Uspizig/WifiWallSwitch/Pictures/230V Module/IMG20230703215954.jpg

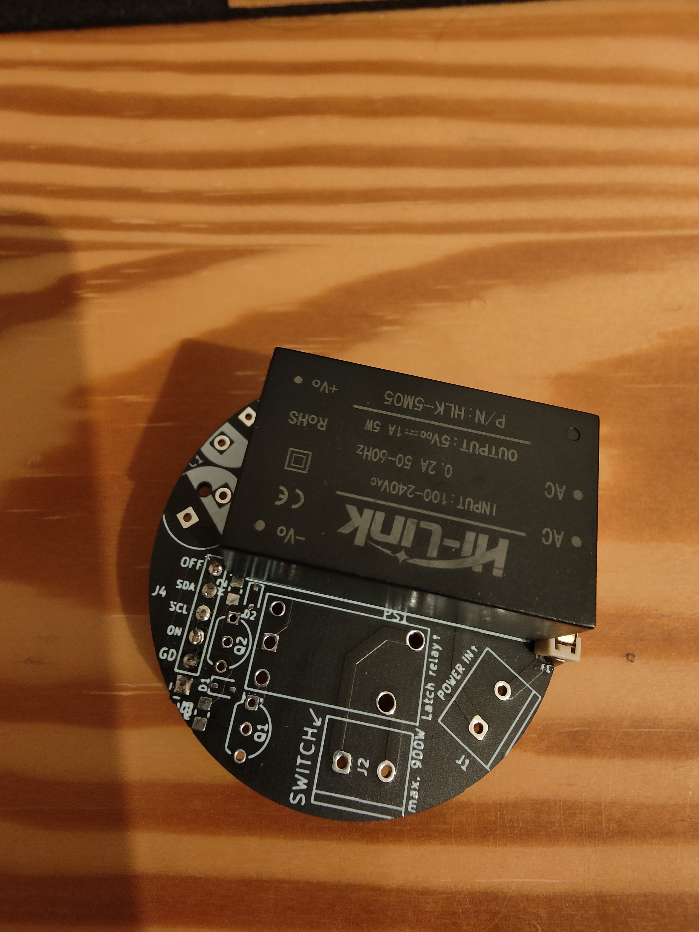
Pictures/230V Module/IMG20230703215954.jpg
