Uspizig/WifiWallSwitch/Pictures/230V Module/IMG20230703220000.jpg

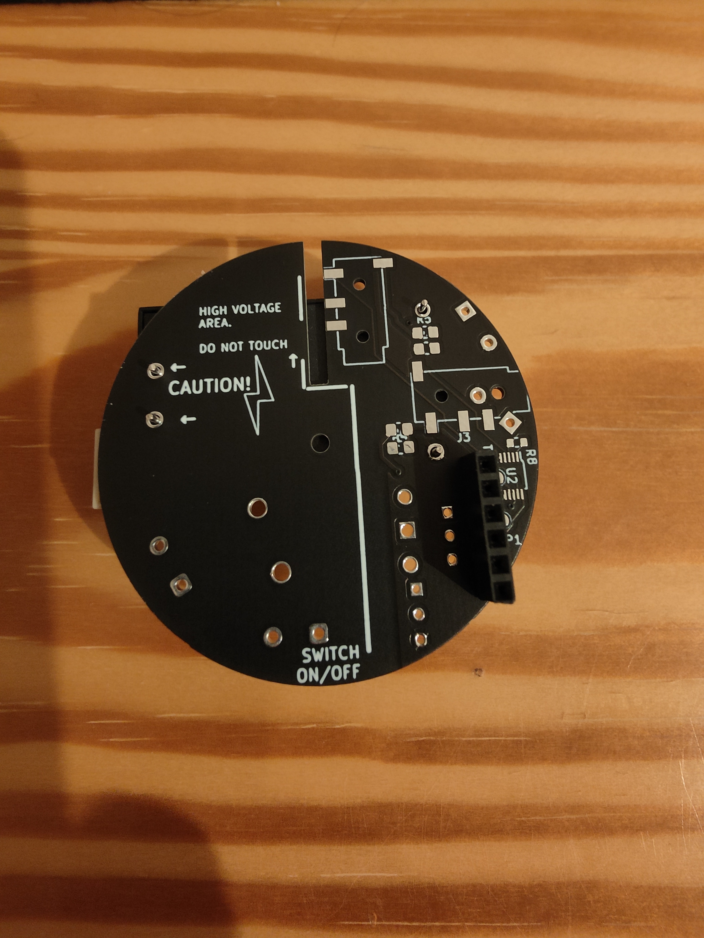
Pictures/230V Module/IMG20230703220000.jpg
