Uspizig/WifiWallSwitch/Pictures/230V Module/IMG20230703220749.jpg

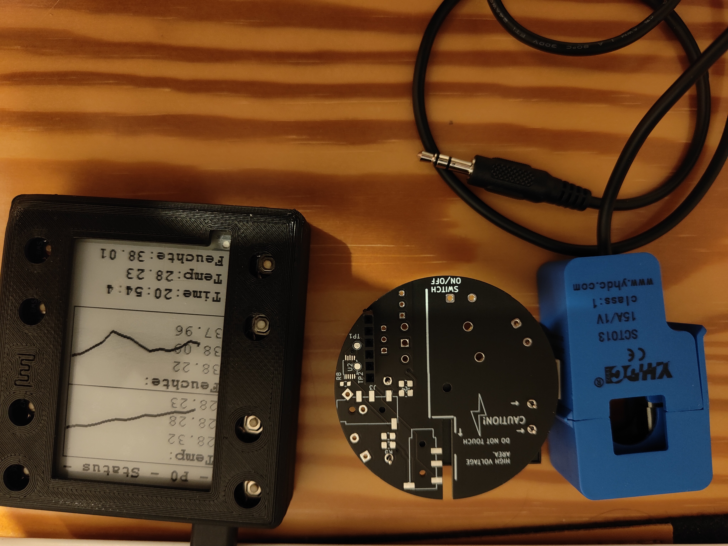
Pictures/230V Module/IMG20230703220749.jpg
