Uspizig/WifiWallSwitch/Pictures/230V Module/IMG20230703220805.jpg

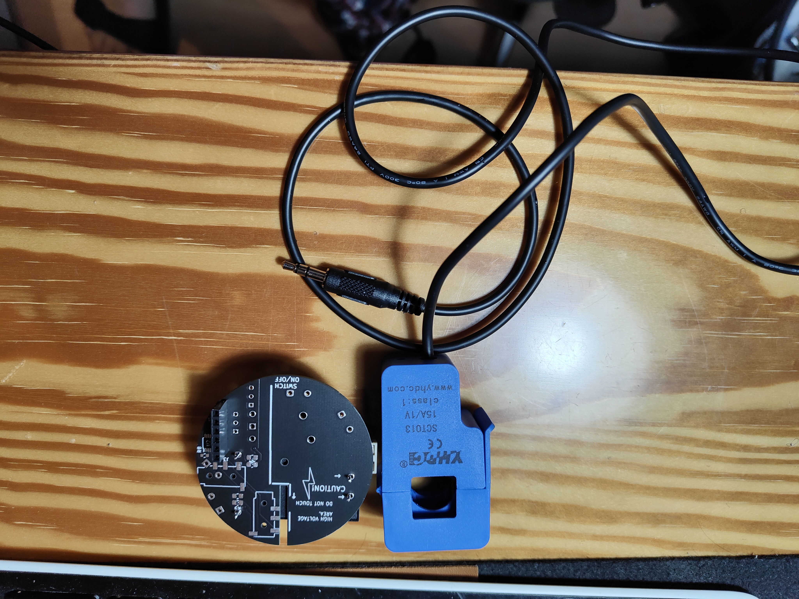
Pictures/230V Module/IMG20230703220805.jpg
