Uspizig/WifiWallSwitch/Pictures/230V Module/IMG20230703220815.jpg

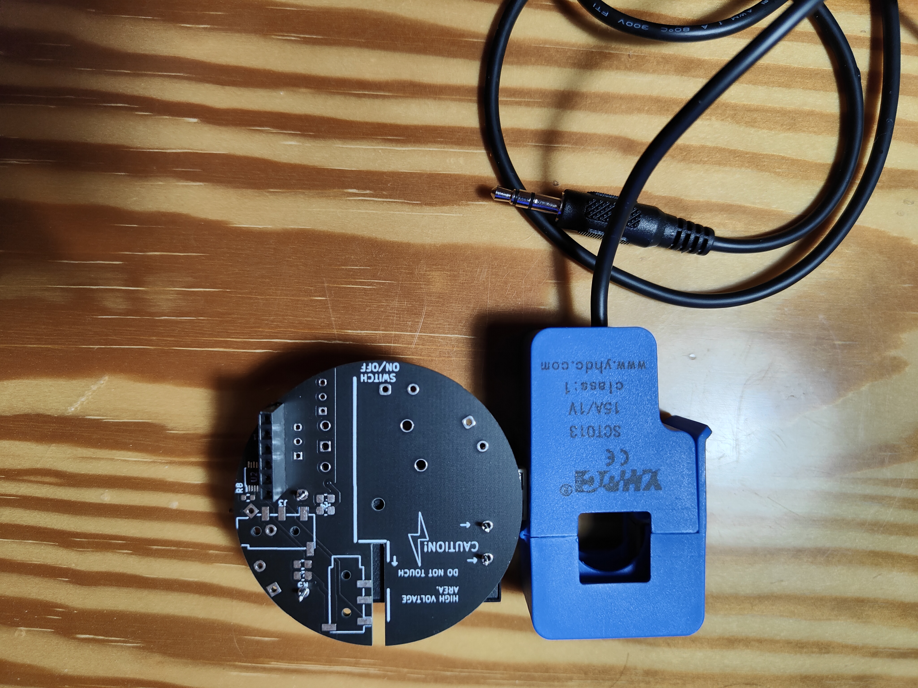
Pictures/230V Module/IMG20230703220815.jpg
