Uspizig/WifiWallSwitch/Pictures/230V Module/IMG20230703220847.jpg

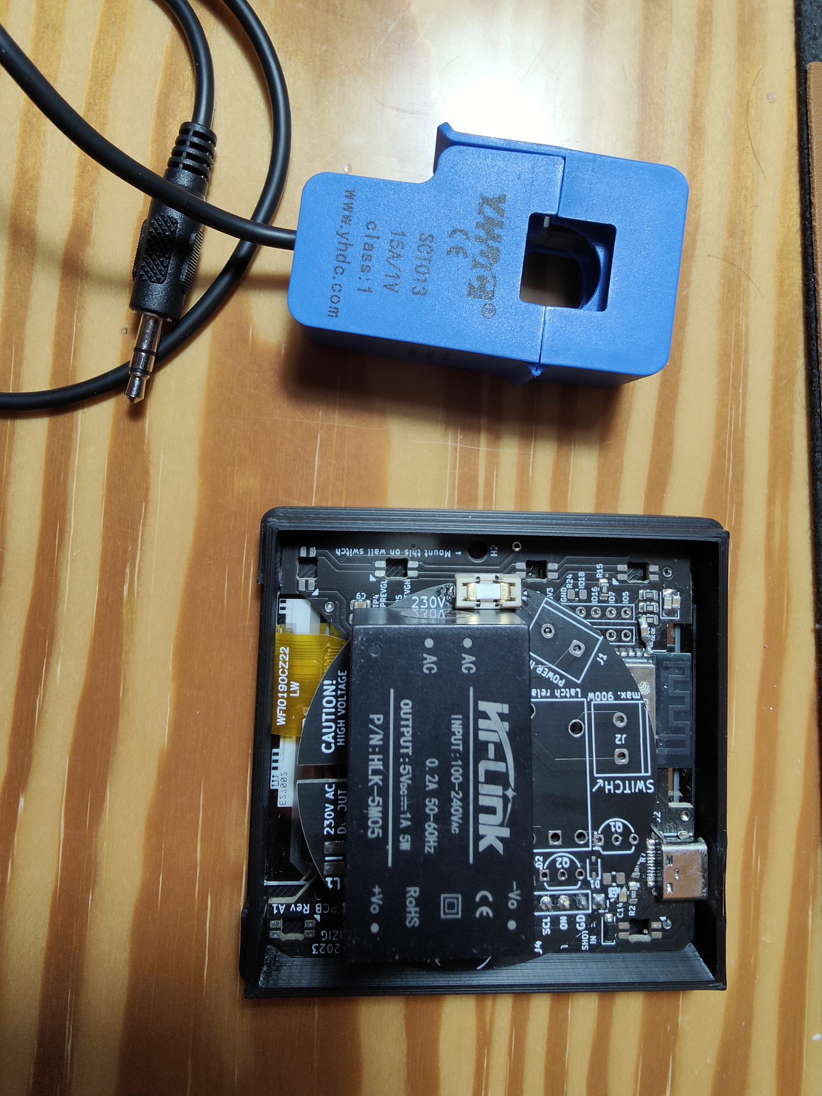
Pictures/230V Module/IMG20230703220847.jpg
