Uspizig/WifiWallSwitch/Pictures/230V Module/IMG20230703220852.jpg

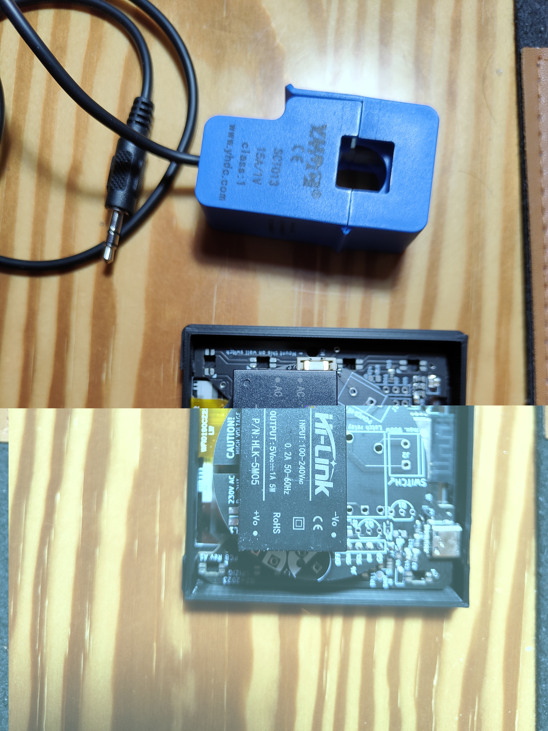
Pictures/230V Module/IMG20230703220852.jpg
