Uspizig/WifiWallSwitch/Pictures/ArduinoBlackCaseButtons/Black.jpg

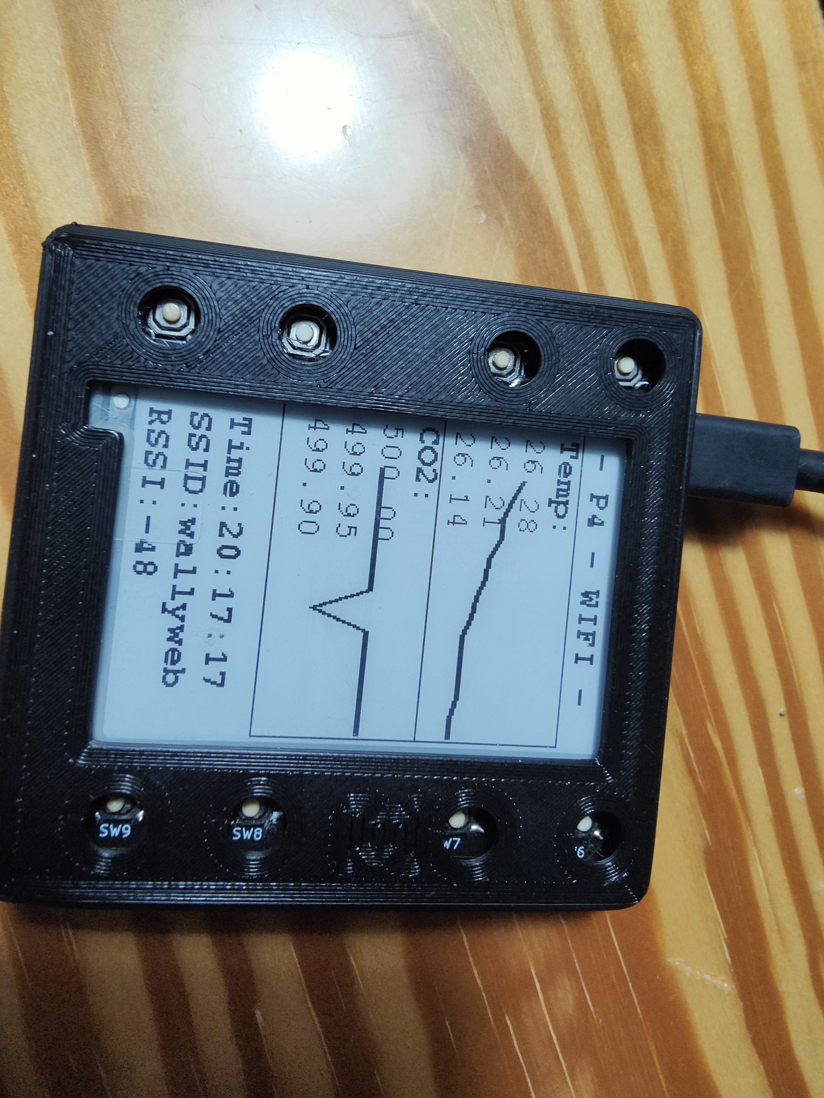
Pictures/ArduinoBlackCaseButtons/Black.jpg
