Uspizig/WifiWallSwitch/Pictures/ArduinoBlackCaseButtons/IMG20230702214540.jpg

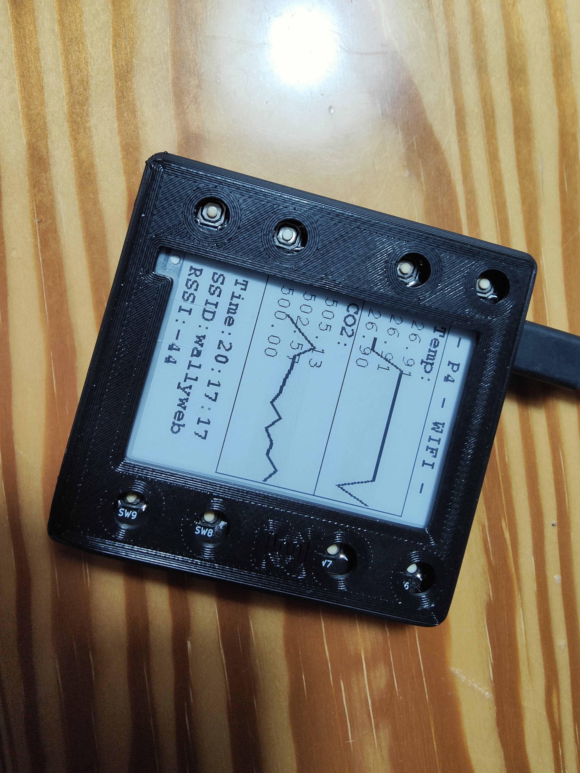
Pictures/ArduinoBlackCaseButtons/IMG20230702214540.jpg
