Uspizig/WifiWallSwitch/Pictures/ArduinoBlackCaseButtons/IMG20230702214551.jpg

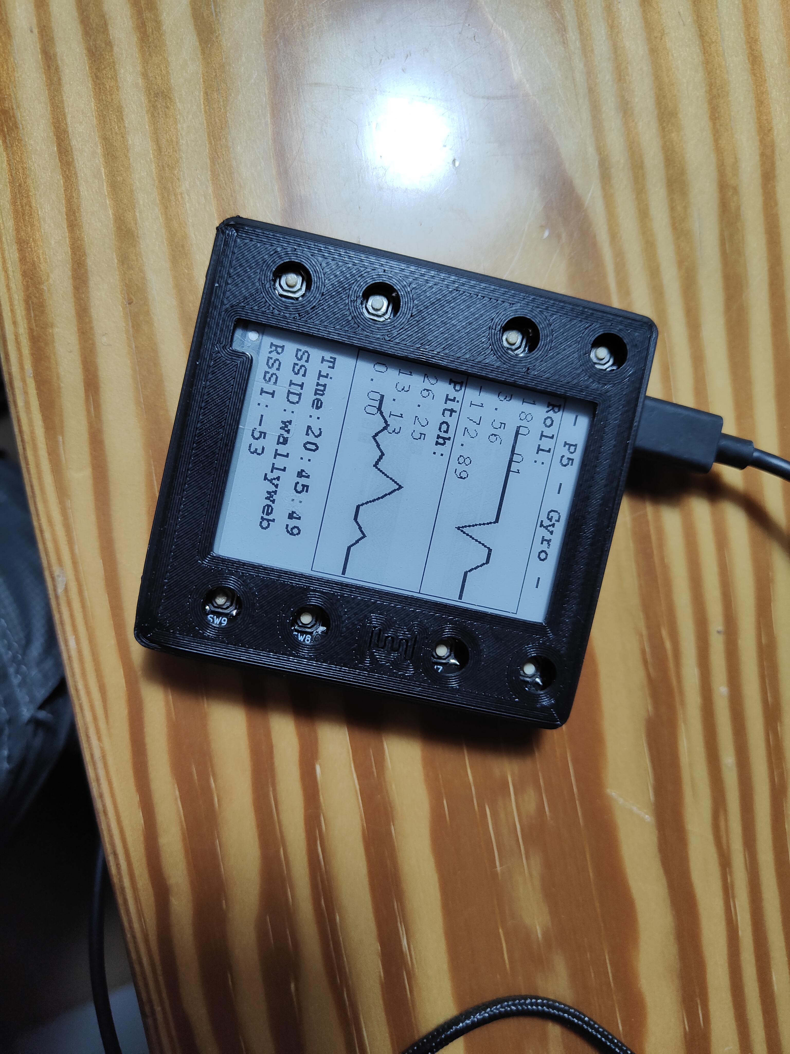
Pictures/ArduinoBlackCaseButtons/IMG20230702214551.jpg
