Uspizig/WifiWallSwitch/Pictures/ArduinoBlackCaseButtons/IMG20230702214604.jpg

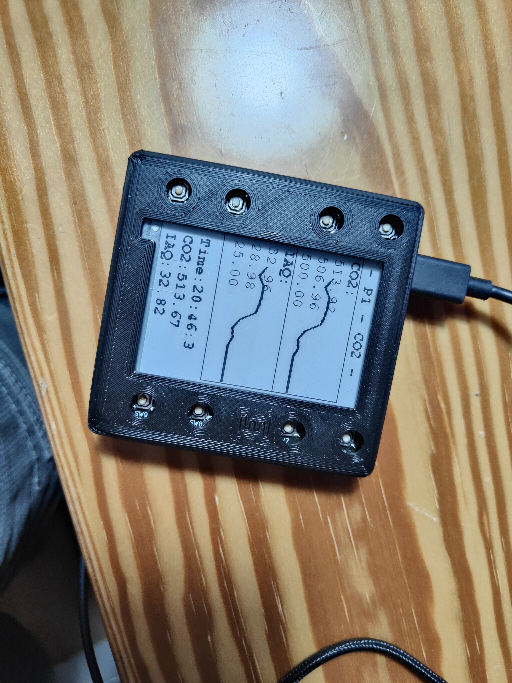
Pictures/ArduinoBlackCaseButtons/IMG20230702214604.jpg
