Uspizig/WifiWallSwitch/Pictures/ArduinoBlackCaseButtons/IMG20230702214607.jpg

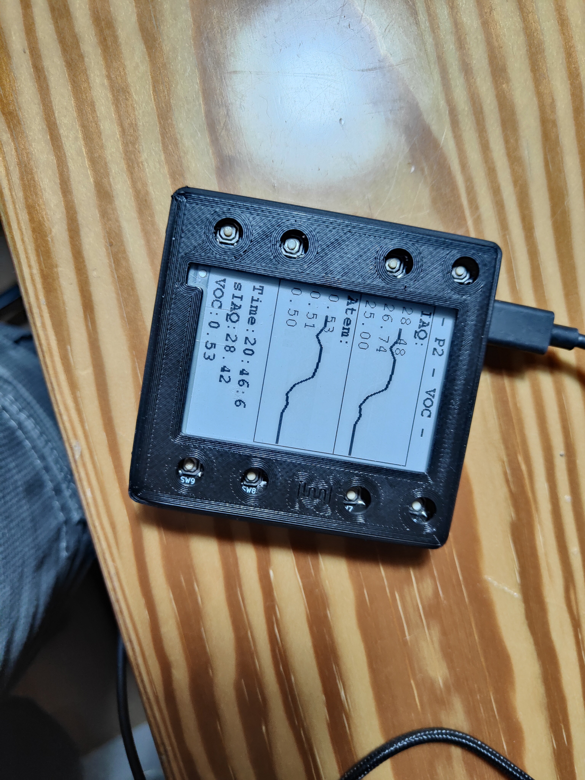
Pictures/ArduinoBlackCaseButtons/IMG20230702214607.jpg
