Uspizig/WifiWallSwitch/Pictures/KiCad3DView/case360.jpg

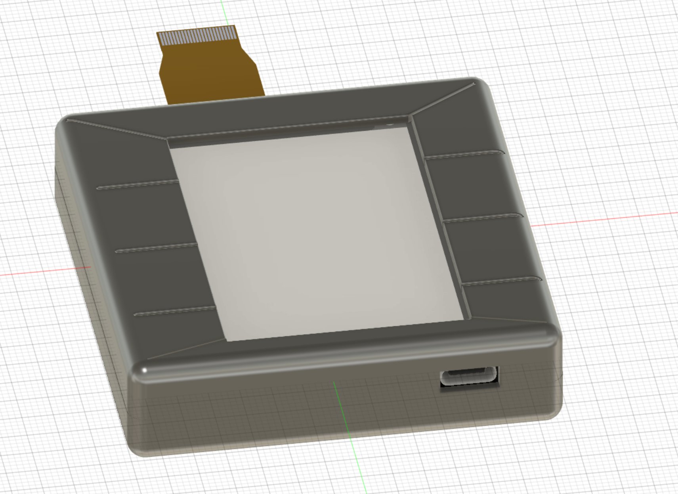
Pictures/KiCad3DView/case360.jpg
