Uspizig/WifiWallSwitch/Pictures/KiCad3DView/casewo.jpg

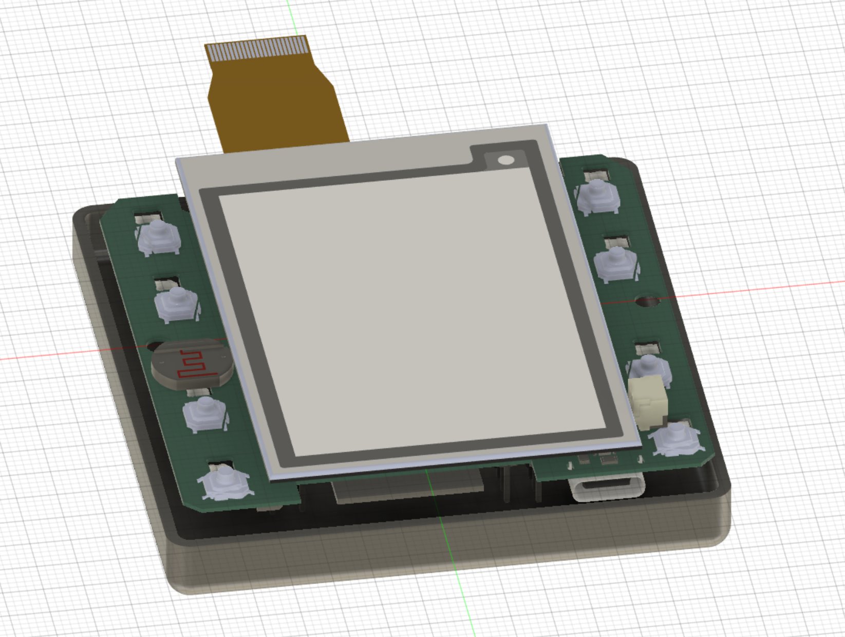
Pictures/KiCad3DView/casewo.jpg
