Uspizig/WifiWallSwitch/Pictures/KiCad3DView/kicad2.jpg

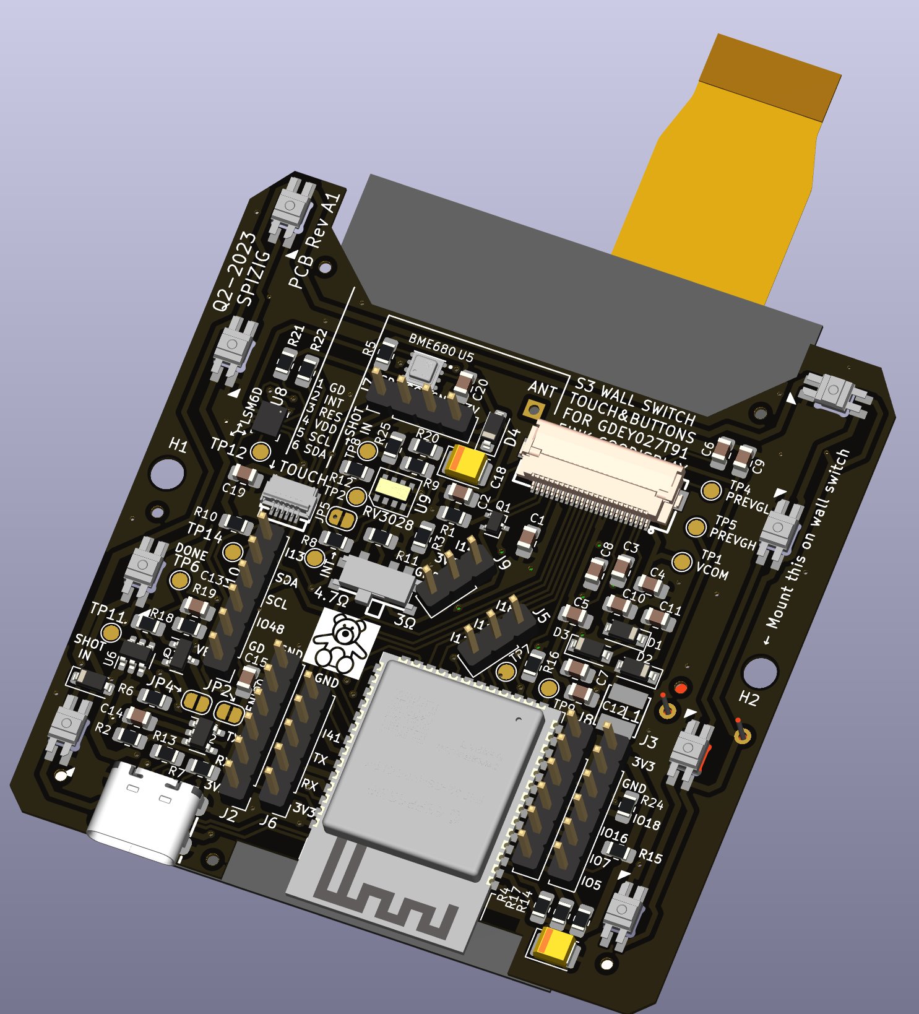
Pictures/KiCad3DView/kicad2.jpg
