Uspizig/WifiWallSwitch/Pictures/KiCad3DView/kicad.jpg

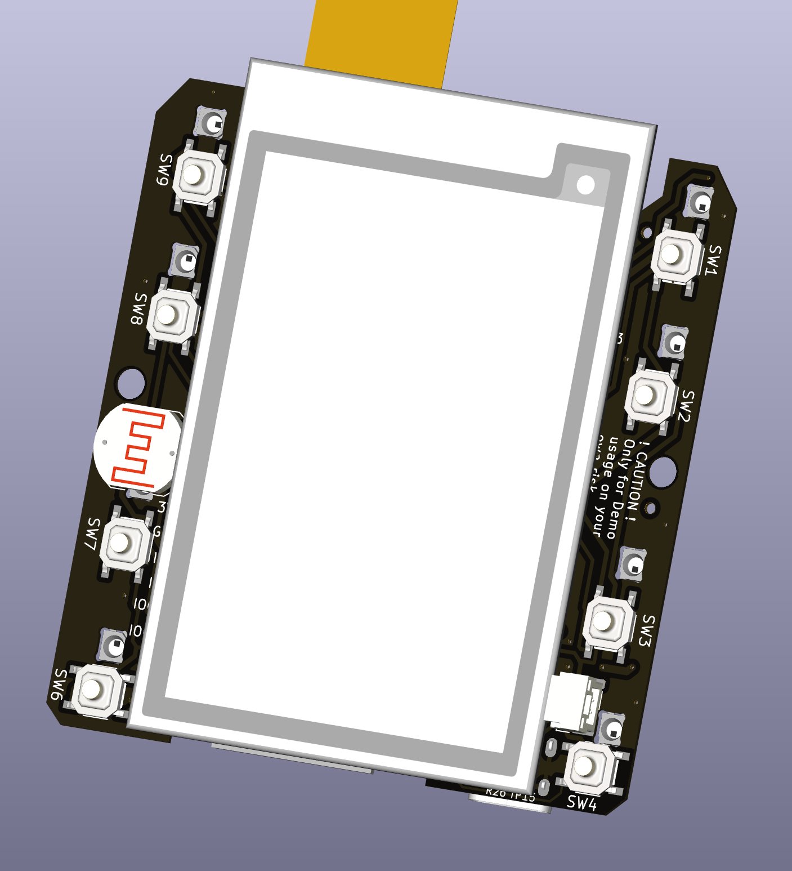
Pictures/KiCad3DView/kicad.jpg
