Uspizig/WifiWallSwitch/Pictures/WhiteHiddenButtonsCase/IMG20240104233957.jpg

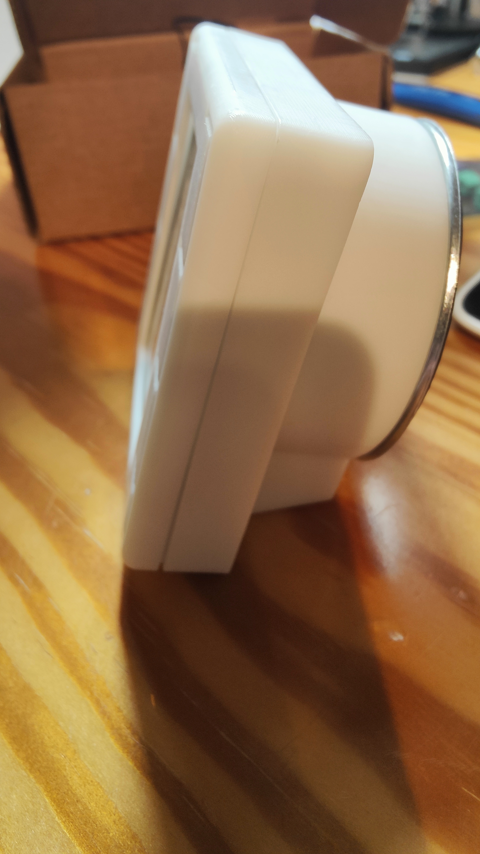
Pictures/WhiteHiddenButtonsCase/IMG20240104233957.jpg
