Uspizig/WifiWallSwitch/Pictures/WhiteHiddenButtonsCase/IMG20240104234006.jpg

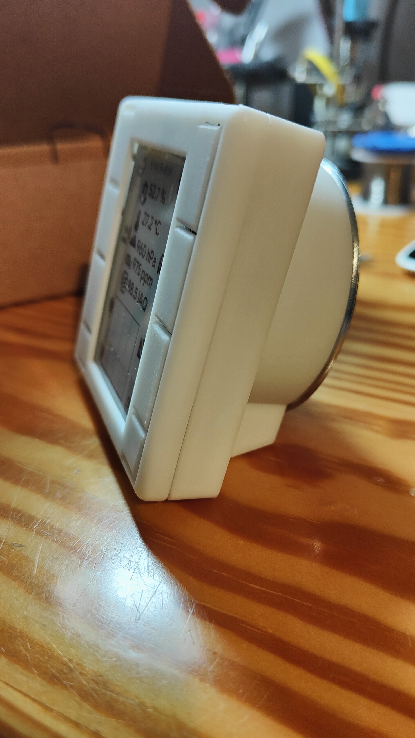
Pictures/WhiteHiddenButtonsCase/IMG20240104234006.jpg
