Uspizig/WifiWallSwitch/Pictures/WhiteHiddenButtonsCase/IMG20240104234016.jpg

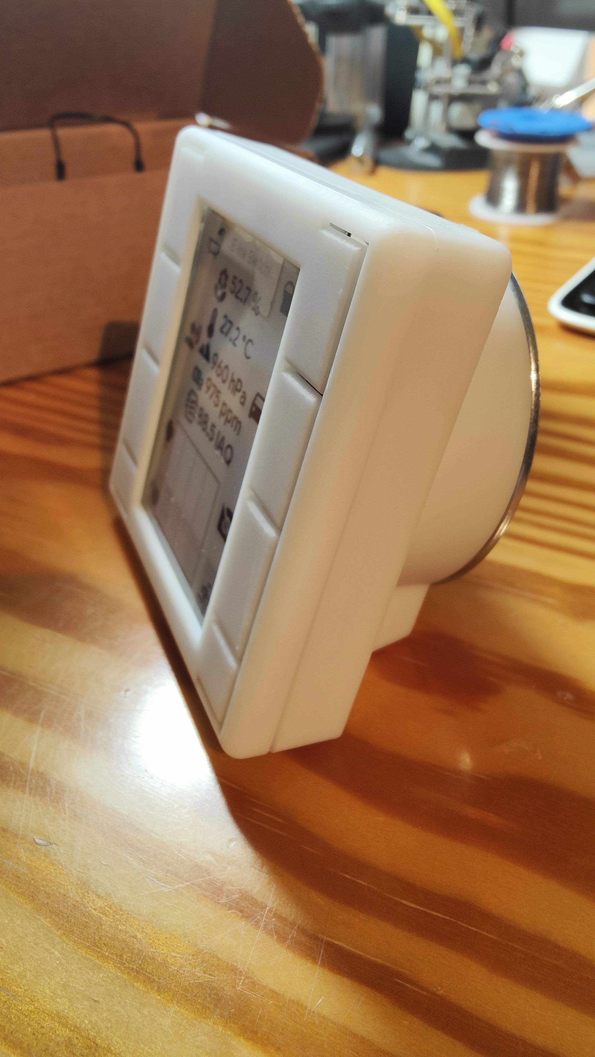
Pictures/WhiteHiddenButtonsCase/IMG20240104234016.jpg
