Uspizig/WifiWallSwitch/Pictures/WhiteHiddenButtonsCase/IMG20240104234021.jpg

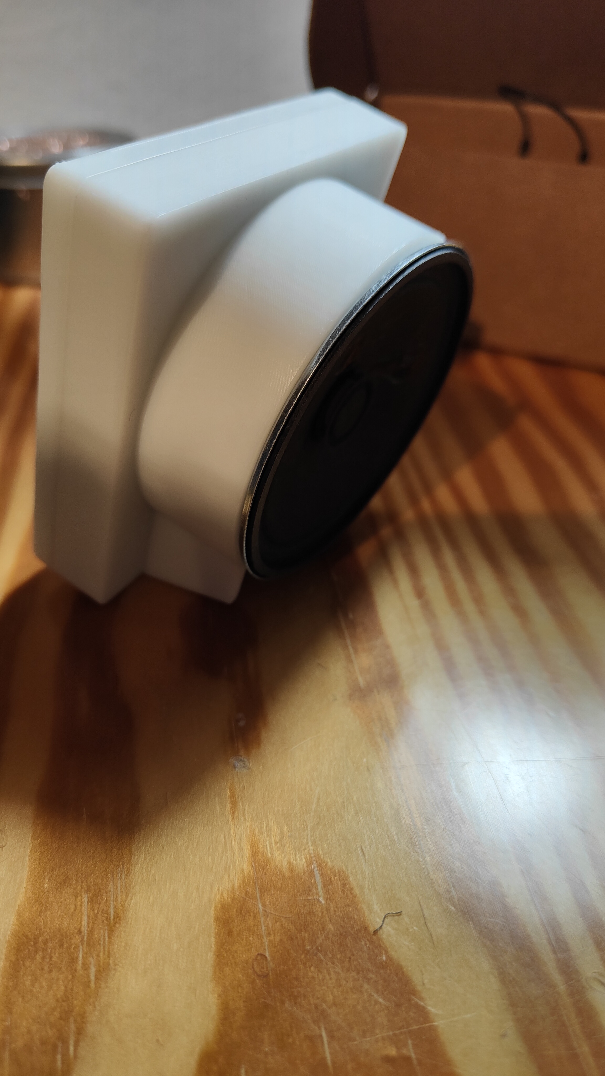
Pictures/WhiteHiddenButtonsCase/IMG20240104234021.jpg
