Uspizig/WifiWallSwitch/Pictures/WhiteHiddenButtonsCase/IMG20240104234024.jpg

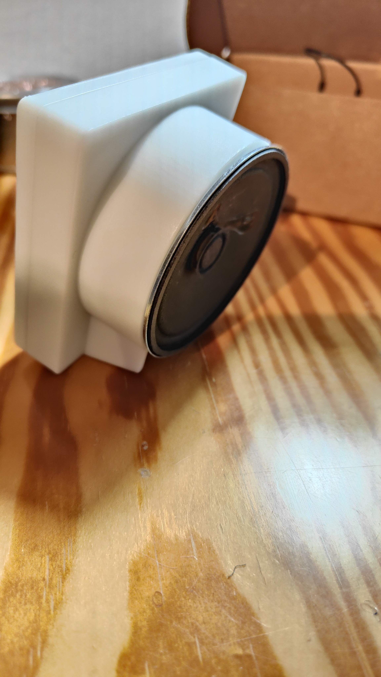
Pictures/WhiteHiddenButtonsCase/IMG20240104234024.jpg
