Uspizig/WifiWallSwitch/Pictures/WhiteHiddenButtonsCase/IMG_20240105_171326.jpg

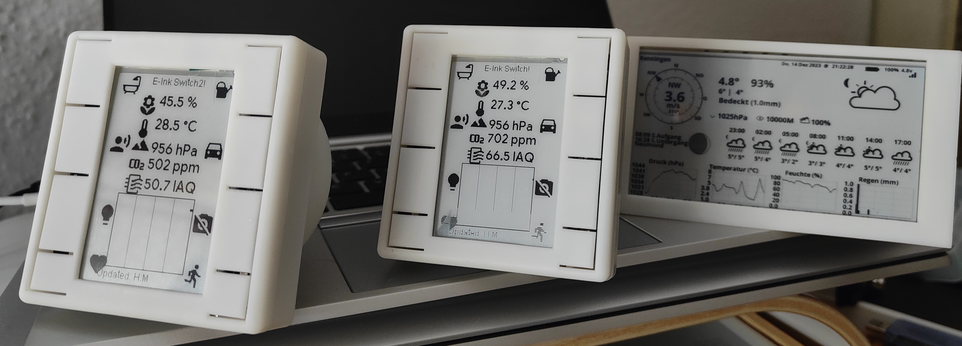
Pictures/WhiteHiddenButtonsCase/IMG_20240105_171326.jpg
