Uspizig/WifiWallSwitch/Pictures/WhiteHiddenButtonsCase/IMG_20240105_184740.jpg

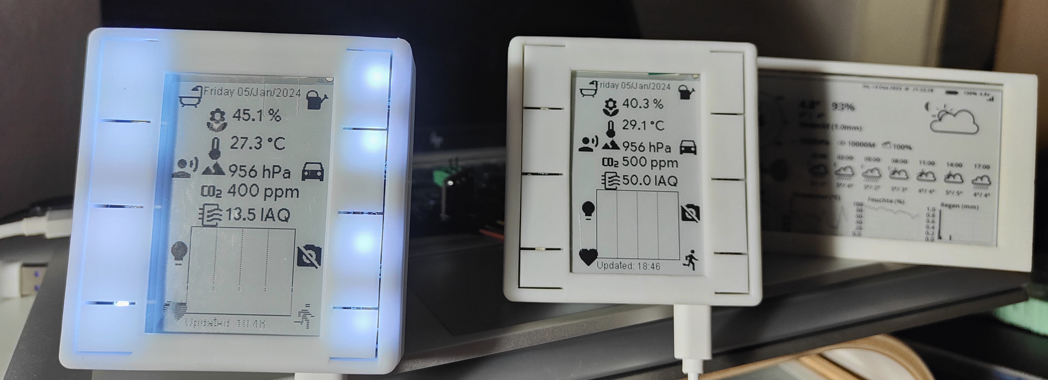
Pictures/WhiteHiddenButtonsCase/IMG_20240105_184740.jpg
