Uspizig/WifiWallSwitch/Pictures/WhiteHiddenButtonsCase/IMG_20240105_184812.jpg

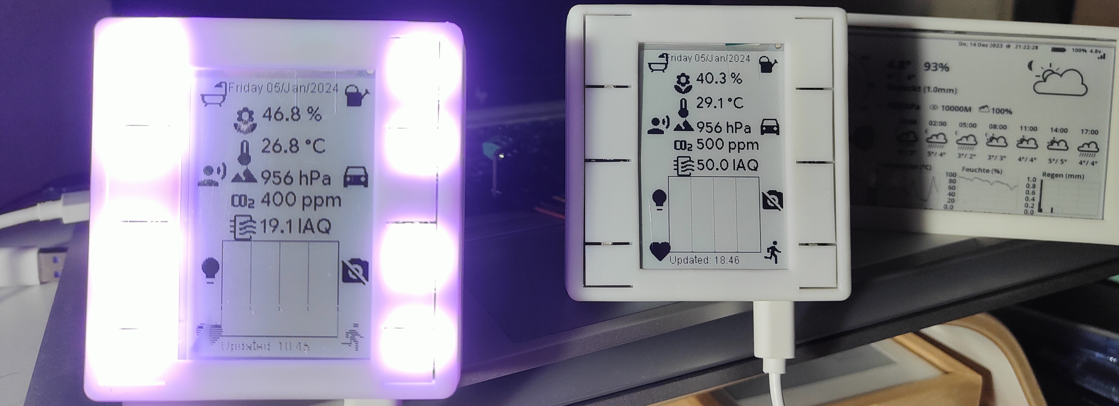
Pictures/WhiteHiddenButtonsCase/IMG_20240105_184812.jpg
