Uspizig/WifiWallSwitch/Pictures/WhiteHiddenButtonsCase/IMG_20240105_184826.jpg

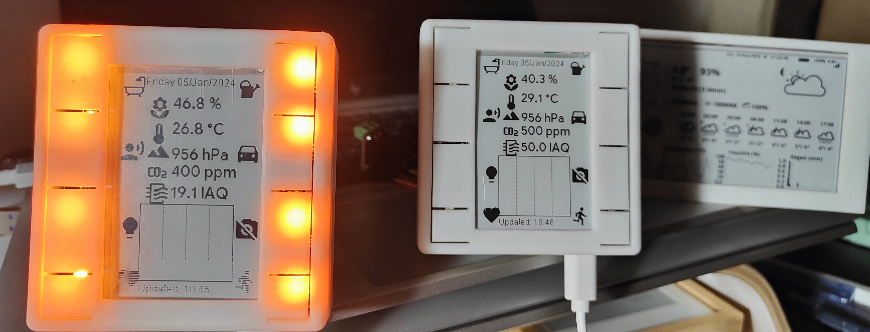
Pictures/WhiteHiddenButtonsCase/IMG_20240105_184826.jpg
