Uspizig/WifiWallSwitch/Pictures/WhiteHiddenButtonsCase/IMG_20240105_184838.jpg

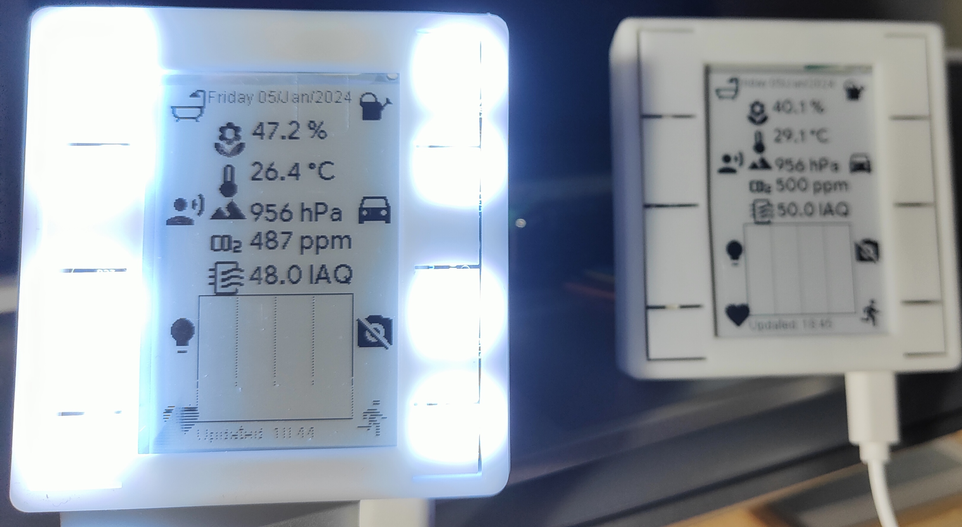
Pictures/WhiteHiddenButtonsCase/IMG_20240105_184838.jpg
