Uspizig/WifiWallSwitch/Pictures/WhiteHiddenButtonsCase/IMG_20240105_184855.jpg

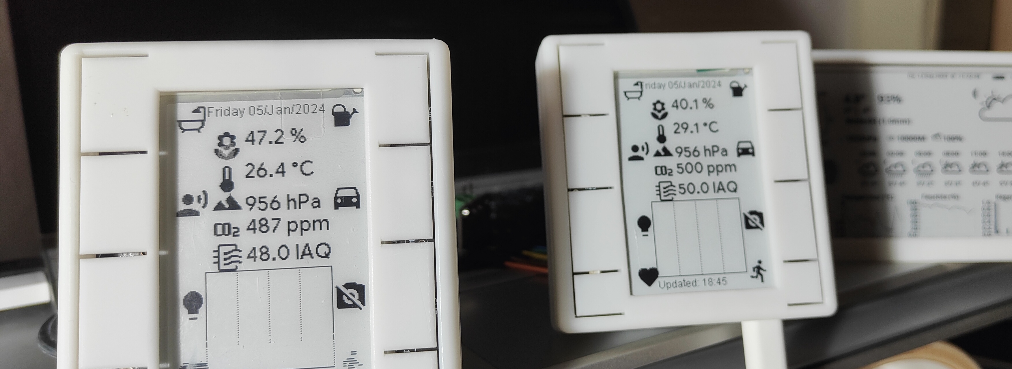
Pictures/WhiteHiddenButtonsCase/IMG_20240105_184855.jpg
