Uspizig/WifiWallSwitch/Pictures/WhiteHiddenButtonsCase/IMG_20240105_184921.jpg

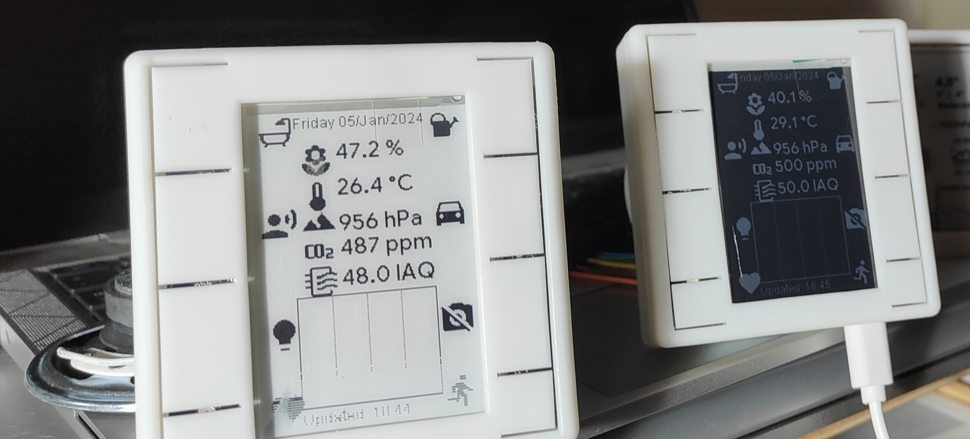
Pictures/WhiteHiddenButtonsCase/IMG_20240105_184921.jpg
