Uspizig/WifiWallSwitch/Hardware/S3-27-epaper-touch-pro/parts/3d/CR1220-2.step

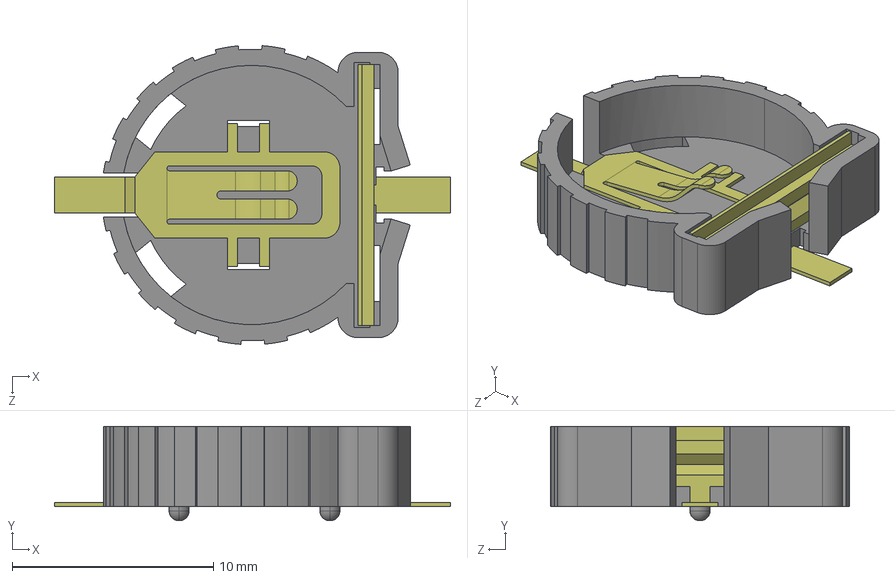
[picture p53: CAD file, 2023-03-05, an earlier design]
Hardware/S3-27-epaper-touch-pro/parts/3d/CR1220-2.step
19.7 x 4.70 x 14.9 mm
