Uspizig/WifiWallSwitch/Hardware/S3-27-epaper-touch-pro/parts/3d/IND_0S282MT_SNL.step

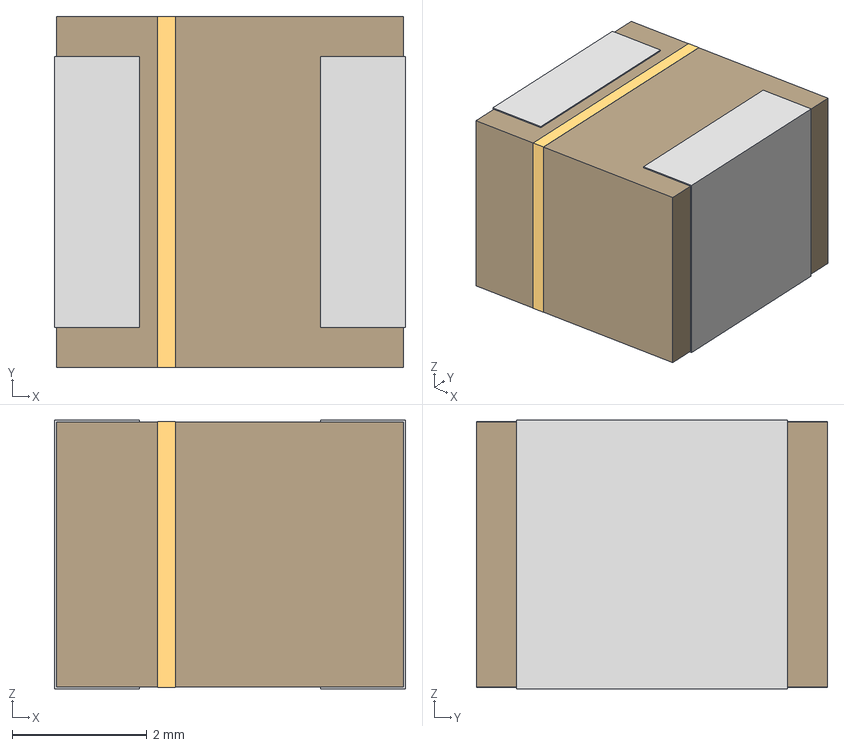
[picture p54: CAD file, 2023-03-05, an earlier design]
Hardware/S3-27-epaper-touch-pro/parts/3d/IND_0S282MT_SNL.step
5.21 x 5.21 x 3.99 mm
