Uspizig/WifiWallSwitch/Hardware/S3-27-epaper-touch-pro/parts/3d/FH12-24S-0.5SH_55_.step

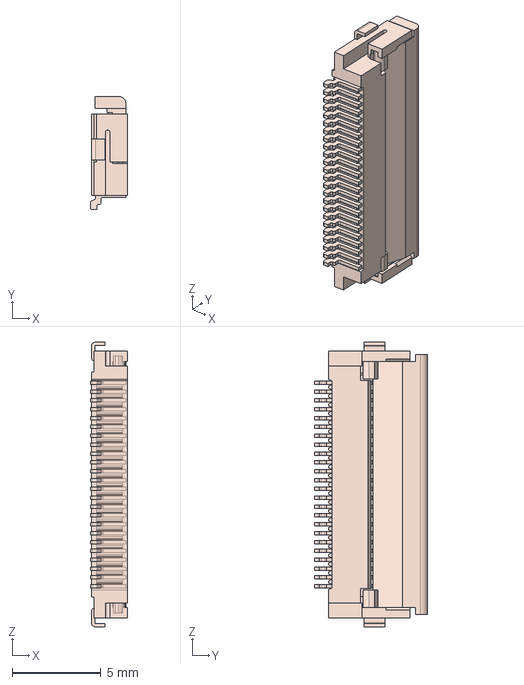
[picture p55: CAD file, 2023-03-05, an earlier design]
Hardware/S3-27-epaper-touch-pro/parts/3d/FH12-24S-0.5SH_55_.step
2.10 x 6.40 x 16.1 mm
