Uspizig/WifiWallSwitch/Software/ARDUINO/EINK_BME680_KEYS/user_kennung.h

//#define debug false
//#define debug true
#define WLAN_SSID       "xxxxx"  //Put your SSID here
#define WLAN_PASS       "xxxxxx"  //Put you wifi password here


//const unsigned long UpdateInterval = (40L * 60L) * 1000000L; //60sec mal 60 = 1h
const unsigned long UpdateInterval = (30L * 60L) * 1000000L; //60sec mal 60 = 2min


//Connection Settings
const char* host = "script.google.com";
const char* googleRedirHost = "script.googleusercontent.com";
const char*  server = "script.google.com";
const int httpsPort = 443;
